sTeeLM/CNCPowerSupply/Simulate/0-30V  可调电压、电流稳压电源套件(1)/元件清单.jpg

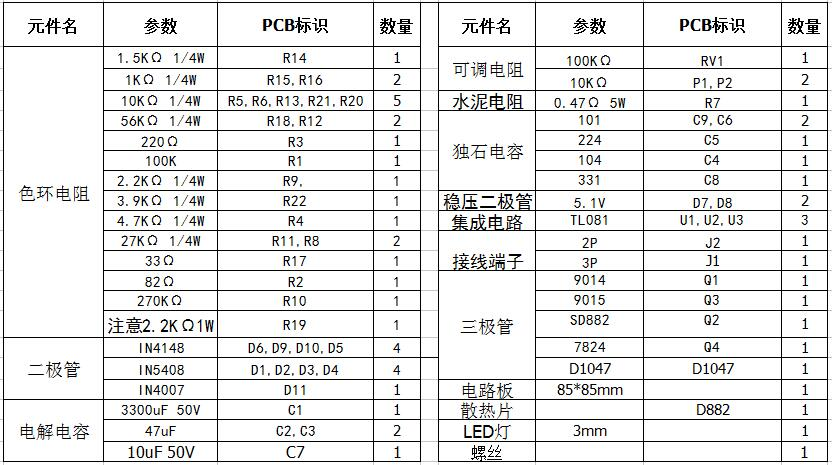
Simulate/0-30V 可调电压、电流稳压电源套件(1)/元件清单.jpg
