sTeeLM/CNCPowerSupply/Source/xmeter/cal_common.h

#ifndef __XMETER_CAL_COMMON_H__
#define __XMETER_CAL_COMMON_H__

#include "xmeter.h"

#include <stdint.h>

extern xmeter_grid_t cal_grid_adc[XMETER_GRID_SIZE];
extern xmeter_grid_t cal_grid_dac[XMETER_GRID_SIZE];

#endif
