sTeeLM/CNCPowerSupply/Source/control/Core/Src/delay.c

#include "delay.h"

uint8_t delay_init(void)
{
  uint8_t i;
  /* Disable TRC */
  CoreDebug->DEMCR &= ~CoreDebug_DEMCR_TRCENA_Msk; // ~0x01000000;
  /* Enable TRC */
  CoreDebug->DEMCR |=  CoreDebug_DEMCR_TRCENA_Msk; // 0x01000000;

  /* Disable clock cycle counter */
  DWT->CTRL &= ~DWT_CTRL_CYCCNTENA_Msk; //~0x00000001;
  /* Enable  clock cycle counter */
  DWT->CTRL |=  DWT_CTRL_CYCCNTENA_Msk; //0x00000001;

  /* Reset the clock cycle counter value */
  DWT->CYCCNT = 0;

     /* 3 NO OPERATION instructions */
  for(i = 0 ; i < 128 ; i ++) {
    __ASM volatile ("NOP");
    __ASM volatile ("NOP");
    __ASM volatile ("NOP");
    __ASM volatile ("NOP");
    __ASM volatile ("NOP");
    __ASM volatile ("NOP");
  }
  /* Check if clock cycle counter has started */
  if(DWT->CYCCNT)
  {
    return 1; /*clock cycle counter started*/
  }
  else
  {
    return 0; /*clock cycle counter not started*/
  }
}
